osresearch/pendant/trinketloader/code.cpp

#include "optiLoader.h"
#define VERBOSE 0

/*
 * readSignature
 * read the bottom two signature bytes (if possible) and return them
 * Note that the highest signature byte is the same over all AVRs so we skip it
 */

uint16_t readSignature (void)
{
  SPI.setClockDivider(CLOCKSPEED_FUSES); 
    
  uint16_t target_type = 0;
  Serial.print("\nReading signature:");
  
  target_type = spi_transaction(0x30, 0x00, 0x01, 0x00);
  target_type <<= 8;
  target_type |= spi_transaction(0x30, 0x00, 0x02, 0x00);
  
  Serial.println(target_type, HEX);
  if (target_type == 0 || target_type == 0xFFFF) {
    if (target_type == 0) {
      Serial.println("  (no target attached?)");
    }
  }
  return target_type;
}

/*
 * findImage
 *
 * given 'signature' loaded with the relevant part of the device signature,
 * search the hex images that we have programmed in flash, looking for one
 * that matches.
 */
const image_t *findImage (uint16_t signature)
{
  const image_t *ip;
  Serial.print("Searching for image: ");
  Serial.println(signature, HEX);

  for (byte i=0; i < NUMIMAGES; i++) {
    ip = images[i];

    if (ip && (pgm_read_word(&ip->image_chipsig) == signature)) {
	Serial.print("  Found \"");
	flashprint(&ip->image_name[0]);
	Serial.print("\" for ");
	flashprint(&ip->image_chipname[0]);
	Serial.println();

	return ip;
    }
  }
  Serial.println(" Not Found");
  return 0;
}

/*
 * programmingFuses
 * Program the fuse/lock bits
 */
boolean programFuses (const byte *fuses)
{
  SPI.setClockDivider(CLOCKSPEED_FUSES); 
    
  byte f;
  Serial.print("\nSetting fuses");

  f = pgm_read_byte(&fuses[FUSE_PROT]);
  if (f) {
    Serial.print("\n  Set Lock Fuse to: ");
    Serial.print(f, HEX);
    Serial.print(" -> ");
    Serial.print(spi_transaction(0xAC, 0xE0, 0x00, f), HEX);
  }
  f = pgm_read_byte(&fuses[FUSE_LOW]);
  if (f) {
    Serial.print("\n  Set Low Fuse to: ");
    Serial.print(f, HEX);
    Serial.print(" -> ");
    Serial.print(spi_transaction(0xAC, 0xA0, 0x00, f), HEX);
  }
  f = pgm_read_byte(&fuses[FUSE_HIGH]);
  if (f) {
    Serial.print("\n  Set High Fuse to: ");
    Serial.print(f, HEX);
    Serial.print(" -> ");
    Serial.print(spi_transaction(0xAC, 0xA8, 0x00, f), HEX);
  }
  f = pgm_read_byte(&fuses[FUSE_EXT]);
  if (f) {
    Serial.print("\n  Set Ext Fuse to: ");
    Serial.print(f, HEX);
    Serial.print(" -> ");
    Serial.print(spi_transaction(0xAC, 0xA4, 0x00, f), HEX);
  }
  Serial.println();
  return true;			/* */
}

/*
 * verifyFuses
 * Verifies a fuse set
 */
boolean verifyFuses (const byte *fuses, const byte *fusemask)
{
  SPI.setClockDivider(CLOCKSPEED_FUSES); 
  byte f;
  Serial.println(F("Verifying fuses..."));
  f = pgm_read_byte(&fuses[FUSE_PROT]);
  if (f) {
    uint8_t readfuse = spi_transaction(0x58, 0x00, 0x00, 0x00);  // lock fuse
    readfuse &= pgm_read_byte(&fusemask[FUSE_PROT]);
    Serial.print(F("\tLock Fuse: ")); Serial.print(f, HEX);  Serial.print(" is "); Serial.println(readfuse, HEX);
    if (readfuse != f) 
      return false;
  }
  f = pgm_read_byte(&fuses[FUSE_LOW]);
  if (f) {
    uint8_t readfuse = spi_transaction(0x50, 0x00, 0x00, 0x00);  // low fuse
    Serial.print(F("\tLow Fuse: 0x"));  Serial.print(f, HEX); Serial.print(" is 0x"); Serial.println(readfuse, HEX);
    readfuse &= pgm_read_byte(&fusemask[FUSE_LOW]);
    if (readfuse != f) 
      return false;
  }
  f = pgm_read_byte(&fuses[FUSE_HIGH]);
  if (f) {
    uint8_t readfuse = spi_transaction(0x58, 0x08, 0x00, 0x00);  // high fuse
    readfuse &= pgm_read_byte(&fusemask[FUSE_HIGH]);
    Serial.print(F("\tHigh Fuse: 0x"));  Serial.print(f, HEX); Serial.print(" is 0x");  Serial.println(readfuse, HEX);
    if (readfuse != f) 
      return false;
  }
  f = pgm_read_byte(&fuses[FUSE_EXT]);
  if (f) {
    uint8_t readfuse = spi_transaction(0x50, 0x08, 0x00, 0x00);  // ext fuse
    readfuse &= pgm_read_byte(&fusemask[FUSE_EXT]);
    Serial.print("\tExt Fuse: 0x"); Serial.print(f, HEX); Serial.print(" is 0x"); Serial.println(readfuse, HEX);
    if (readfuse != f) 
      return false;
  }
  Serial.println();
  return true;			/* */
}



/*
 * readImagePage
 *
 * Read a page of intel hex image from a string in pgm memory.
*/

// Returns number of bytes decoded
const byte * readImagePage (const byte *hextext, uint16_t pageaddr, uint8_t pagesize, byte *page)
{
  
  uint16_t len;
  uint8_t page_idx = 0;
  const byte *beginning = hextext;
  
  byte b, cksum = 0;

  //Serial.print("page size = "); Serial.println(pagesize, DEC);

  // 'empty' the page by filling it with 0xFF's
  for (uint8_t i=0; i<pagesize; i++)
    page[i] = 0xFF;

  while (1) {
    uint16_t lineaddr;
    
      // read one line!
    if (pgm_read_byte(hextext++) != ':') {
      fatal("No colon?");
      break;
    }
    // Read the byte count into 'len'
    len = hexton(pgm_read_byte(hextext++));
    len = (len<<4) + hexton(pgm_read_byte(hextext++));
    cksum = len;
    
    // read high address byte
    b = hexton(pgm_read_byte(hextext++));  
    b = (b<<4) + hexton(pgm_read_byte(hextext++));
    cksum += b;
    lineaddr = b;
    
    // read low address byte
    b = hexton(pgm_read_byte(hextext++)); 
    b = (b<<4) + hexton(pgm_read_byte(hextext++));
    cksum += b;
    lineaddr = (lineaddr << 8) + b;
    
    if (lineaddr >= (pageaddr + pagesize)) {
      return beginning;
    }

    b = hexton(pgm_read_byte(hextext++)); // record type 
    b = (b<<4) + hexton(pgm_read_byte(hextext++));
    cksum += b;
    //Serial.print("Record type "); Serial.println(b, HEX);
    if (b == 0x1) { 
     // end record!
     break;
    } 
#if VERBOSE
    Serial.print("\nLine address =  0x"); Serial.println(lineaddr, HEX);      
    Serial.print("Page address =  0x"); Serial.println(pageaddr, HEX);      
#endif
    for (byte i=0; i < len; i++) {
      // read 'n' bytes
      b = hexton(pgm_read_byte(hextext++));
      b = (b<<4) + hexton(pgm_read_byte(hextext++));
      
      cksum += b;
#if VERBOSE
      Serial.print(b, HEX);
      Serial.write(' ');
#endif

      page[page_idx] = b;
      page_idx++;

      if (page_idx > pagesize) {
          fatal("Too much code");
	  break;
      }
    }
    b = hexton(pgm_read_byte(hextext++));  // chxsum
    b = (b<<4) + hexton(pgm_read_byte(hextext++));
    cksum += b;
    if (cksum != 0) {
      fatal("Bad checksum: ");
      Serial.print(cksum, HEX);
    }
    if (pgm_read_byte(hextext++) != '\n') {
      fatal("No end of line");
      break;
    }
#if VERBOSE
    Serial.println();
    Serial.println(page_idx, DEC);
#endif
    if (page_idx == pagesize) 
      break;
  }
#if VERBOSE
  Serial.print("\n  Total bytes read: ");
  Serial.println(page_idx, DEC);
#endif
  return hextext;
}

// Send one byte to the page buffer on the chip
void flashWord (uint8_t hilo, uint16_t addr, uint8_t data) {
#if VERBOSE
  Serial.print(data, HEX);  Serial.print(':');
  Serial.print(spi_transaction(0x40+8*hilo,  addr>>8 & 0xFF, addr & 0xFF, data), HEX);
  Serial.print(" ");
#else
  spi_transaction(0x40+8*hilo, addr>>8 & 0xFF, addr & 0xFF, data);
#endif
}

// Basically, write the pagebuff (with pagesize bytes in it) into page $pageaddr
boolean flashPage (const byte *pagebuff, uint16_t pageaddr, uint8_t pagesize) {  
  SPI.setClockDivider(CLOCKSPEED_FLASH); 

#if VERBOSE
  Serial.print("Flashing page "); Serial.println(pageaddr, HEX);
#endif
  for (uint16_t i=0; i < pagesize/2; i++) {
    
#if VERBOSE
    Serial.print(pagebuff[2*i], HEX); Serial.print(' ');
    Serial.print(pagebuff[2*i+1], HEX); Serial.print(' ');
    if ( i % 16 == 15) Serial.println();
#endif

    flashWord(LOW, i, pagebuff[2*i]);
    flashWord(HIGH, i, pagebuff[2*i+1]);
  }

  // page addr is in bytes, byt we need to convert to words (/2)
  pageaddr = (pageaddr/2) & ~(pagesize/2 - 1);
  uint16_t commitreply = spi_transaction(0x4C, (pageaddr >> 8) & 0xFF, pageaddr & 0xFF, 0);

#if VERBOSE
  Serial.print("  Commit Page: 0x");  Serial.print(pageaddr, HEX);
  Serial.print(" -> 0x"); Serial.println(commitreply, HEX);
#endif
  if (commitreply != pageaddr) 
    return false;

  busyWait();
  
  return true;
}

// verifyImage does a byte-by-byte verify of the flash hex against the chip
// Thankfully this does not have to be done by pages!
// returns true if the image is the same as the hextext, returns false on any error
boolean verifyImage (const byte *hextext)  {
  SPI.setClockDivider(CLOCKSPEED_FLASH); 

  uint16_t len;
  byte b, cksum = 0;

  while (1) {
    uint16_t lineaddr;
    
      // read one line!
    if (pgm_read_byte(hextext++) != ':') {
      fatal("No colon");
      return false;
    }
    len = hexton(pgm_read_byte(hextext++));
    len = (len<<4) + hexton(pgm_read_byte(hextext++));
    cksum = len;

    b = hexton(pgm_read_byte(hextext++)); // record type 
    b = (b<<4) + hexton(pgm_read_byte(hextext++));
    cksum += b;
    lineaddr = b;
    b = hexton(pgm_read_byte(hextext++)); // record type
    b = (b<<4) + hexton(pgm_read_byte(hextext++));
    cksum += b;
    lineaddr = (lineaddr << 8) + b;
    
    b = hexton(pgm_read_byte(hextext++)); // record type 
    b = (b<<4) + hexton(pgm_read_byte(hextext++));
    cksum += b;

    //Serial.print("Record type "); Serial.println(b, HEX);
    if (b == 0x1) { 
     // end record!
     break;
    } 
    
    for (byte i=0; i < len; i++) {
      // read 'n' bytes
      b = hexton(pgm_read_byte(hextext++));
      b = (b<<4) + hexton(pgm_read_byte(hextext++));
      cksum += b;
      
#if VERBOSE
      Serial.print("$");
      Serial.print(lineaddr, HEX);
      Serial.print(":0x");
      Serial.print(b, HEX);
      Serial.write(" ? ");
#endif

      // verify this byte!
      if (lineaddr % 2) {
        // for 'high' bytes:
        if (b != (spi_transaction(0x28, lineaddr >> 9, lineaddr / 2, 0) & 0xFF)) {
          Serial.print("verification error at address 0x"); Serial.print(lineaddr, HEX);
          Serial.print(" Should be 0x"); Serial.print(b, HEX); Serial.print(" not 0x");
          Serial.println((spi_transaction(0x28, lineaddr >> 9, lineaddr / 2, 0) & 0xFF), HEX);
          return false;
        }
      } else {
        // for 'low bytes'
        if (b != (spi_transaction(0x20, lineaddr >> 9, lineaddr / 2, 0) & 0xFF)) {
          Serial.print("verification error at address 0x"); Serial.print(lineaddr, HEX);
          Serial.print(" Should be 0x"); Serial.print(b, HEX); Serial.print(" not 0x");
          Serial.println((spi_transaction(0x20, lineaddr >> 9, lineaddr / 2, 0) & 0xFF), HEX);
          return false;
        }
      } 
      lineaddr++;  
    }
    
    b = hexton(pgm_read_byte(hextext++));  // chxsum
    b = (b<<4) + hexton(pgm_read_byte(hextext++));
    cksum += b;
    if (cksum != 0) {
      fatal("Bad checksum: ");
      Serial.print(cksum, HEX);
      return false;
    }
    if (pgm_read_byte(hextext++) != '\n') {
      fatal("No end of line");
      return false;
    }
  }
  return true;
}


// Send the erase command, then busy wait until the chip is erased

void eraseChip(void) {
  SPI.setClockDivider(CLOCKSPEED_FUSES); 
    
  spi_transaction(0xAC, 0x80, 0, 0);	// chip erase    
  busyWait();
}

// Simply polls the chip until it is not busy any more - for erasing and programming
void busyWait(void)  {
  byte busybit;
  do {
    busybit = spi_transaction(0xF0, 0x0, 0x0, 0x0);
    //Serial.print(busybit, HEX);
  } while (busybit & 0x01);
}


/*
 * Functions specific to ISP programming of an AVR
 */
uint16_t spi_transaction (uint8_t a, uint8_t b, uint8_t c, uint8_t d) {

  SPI.transfer(a); 
Serial.print("SPI tx "); Serial.println(a, HEX);

  uint32_t x = SPI.transfer(b);
Serial.print("SPI tx "); Serial.print(b, HEX);
Serial.print(" rx "); Serial.println(x, HEX);

  uint32_t y = SPI.transfer(c);
Serial.print("SPI tx "); Serial.print(c, HEX);
Serial.print(" rx "); Serial.println(y, HEX);

  uint32_t z = SPI.transfer(d);
Serial.print("SPI tx "); Serial.print(d, HEX);
Serial.print(" rx "); Serial.println(z, HEX);

  return 0xFFFFFF & ((x<<16) + (y<<8) + (z<<0));
}
