osresearch/pendant/trinketloader/images.cpp

#include "optiLoader.h"

const image_t PROGMEM image_328 = {
    {"blankfull.hex"},
    {"attiny85"},
    0x930B,				/* Signature bytes for attimny85 */
    {0, 0xF1, 0xD5, 0x06},            // pre program fuses (prot/lock, low, high, ext)
    {0, 0, 0, 0},            // post program fuses
    {0x3F, 0xFF, 0xFF, 0x07},           // fuse mask
    8192,     // size of chip flash in bytes
    64,   // size in bytes of flash page
    {
":100000007FCA7FCA7FCA7FCA7FCA7FCA7FCA7FCAA8\n"
":100010007FCAF89400C0000000000000000000004B\n"
":1000200000000000000000000000000000000000D0\n"
":1000300000000000000000000000000000000000C0\n"
":1015000033C05FC08BC05DC05CC05BC05AC059C0F7\n"
":1015100058C057C056C055C054C053C052C009022D\n"
":1015200012000101008032090400000000000000E8\n"
":1015300012011001FF00000881179F0C0501010234\n"
":10154000000110035400720069006E006B0065001A\n"
":1015500074001203410064006100660072007500AF\n"
":10156000690074000403090411241FBECFE5D2E012\n"
":10157000DEBFCDBF84B7877F84BF88E10FB6F89404\n"
":1015800081BD11BC0FBE91E080E80FB6F89486BD16\n"
":1015900096BD0FBE0AEA0F9310E0A0E6B0E0E4EDBE\n"
":1015A000FFE102C005900D92A236B107D9F721E004\n"
":1015B000A2E6B0E001C01D92A732B207E1F7E7D37F\n"
":1015C00007C59ECFA82FB92F80E090E041E050EAF8\n"
":1015D000609530E009C02D9182279795879510F08E\n"
":1015E00084279527305EC8F36F5FA8F30895EADF7C\n"
":1015F0008D939D930895A6E088279927AA9569F071\n"
":101600000197E1F3B399FCCFB39BFECF81E099271B\n"
":10161000A6B3019611F0A871D9F70895CF93CFB76B\n"
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
":101F80000150110991F71F2D8FEF8F0D81BF21B7E0\n"
":101F900030E0812F90E001968217930784F02BDBCD\n"
":101FA0008453994097FF03C09195819591098C17AF\n"
":101FB0009D0714F4F1B6EC0181B78F5FE7CFF1BE56\n"
":101FC000DF91CF911F910F91FF90EF90DF900895D7\n"
":041FD000F894FFCFB3\n"
":021FD400FF5AB2\n"
//":0400000300001500E4\n"
":00000001FF\n"
}
};


/*
 * Table of defined images
 */
const image_t * const images[] = {
  &image_328,
};

const uint8_t NUMIMAGES = sizeof(images)/sizeof(images[0]);
