osresearch/pendant/trinketloader/optiLoader.h

#include <WProgram.h>
#include <avr/pgmspace.h>
#include "SPI.h"

#ifndef _OPTILOADER_H
#define _OPTILOADER_H

#define FUSE_PROT 0			/* memory protection */
#define FUSE_LOW 1			/* Low fuse */
#define FUSE_HIGH 2			/* High fuse */
#define FUSE_EXT 3			/* Extended fuse */

// You may want to tweak these based on whether your chip is
// using an internal low-speed crystal
#define CLOCKSPEED_FUSES   SPI_CLOCK_DIV128 
#define CLOCKSPEED_FLASH   SPI_CLOCK_DIV8

#define LED_ERR 8
#define LED_PROGMODE 9

typedef struct image {
    char image_name[30];	       /* Ie "optiboot_diecimila.hex" */
    char image_chipname[12];	       /* ie "atmega168" */
    uint16_t image_chipsig;	       /* Low two bytes of signature */
    byte image_progfuses[5];	       /* fuses to set during programming */
    byte image_normfuses[5];	       /* fuses to set after programming */
    byte fusemask[4];
    uint16_t chipsize;
    byte image_pagesize;	       /* page size for flash programming */
    byte image_hexcode[15500];	       /* intel hex format image (text) */
} image_t;

typedef struct alias {
  char image_chipname[12];
  uint16_t image_chipsig;
  image_t * alias_image;
} alias_t;

/*
 * Bootload images.
 * These are the intel Hex files produced by the optiboot makefile,
 * with a small amount of automatic editing to turn them into C strings,
 * and a header attched to identify them
 */

extern const image_t * const images[];
extern const uint8_t NUMIMAGES;


// Useful message printing definitions

#define debug(string) // flashprint(PSTR(string));
extern void __attribute__((__noreturn__)) fatal(const char *string);


void pulse (int pin, int times);
void flashprint (const char p[]);


uint16_t spi_transaction (uint8_t a, uint8_t b, uint8_t c, uint8_t d);
const image_t *findImage (uint16_t signature);


uint16_t readSignature (void);
boolean programFuses (const byte *fuses);
void eraseChip(void);
boolean verifyImage (const byte *hextext);
void busyWait(void);
boolean flashPage (const byte *pagebuff, uint16_t pageaddr, uint8_t pagesize);
byte hexton (byte h);
const byte * readImagePage (const byte *hextext, uint16_t pageaddr, uint8_t pagesize, byte *page);
boolean verifyFuses (const byte *fuses, const byte *fusemask);
void error(char *string);

#endif
